UncleCJ/DTMF-to-joystick-adapter/schematic/DTMF-to-joystick-adapter.kicad_sch

## KiCad design schematic/DTMF-to-joystick-adapter.kicad_sch (2025-05-23)

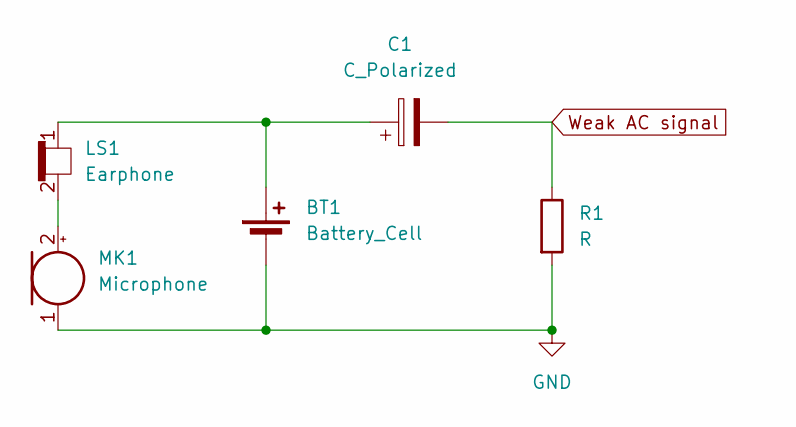
[picture p13: schematic DTMF-to-joystick-adapter.kicad_sch]

Parts:
BT1: Battery_Cell
C1: C_Polarized
LS1: Earphone
MK1: Microphone
R1: R

Connections:
GND: BT1.2 (-), MK1.1 (-), R1.2
unnamed: BT1.1 (+), C1.1, LS1.1 (-)
unnamed: LS1.2 (+), MK1.2 (+)
Weak AC signal: C1.2, R1.1
